lexx-polarnet-pl/AquaPi/Doc/html/hardware/ADS1115-ui.jpg

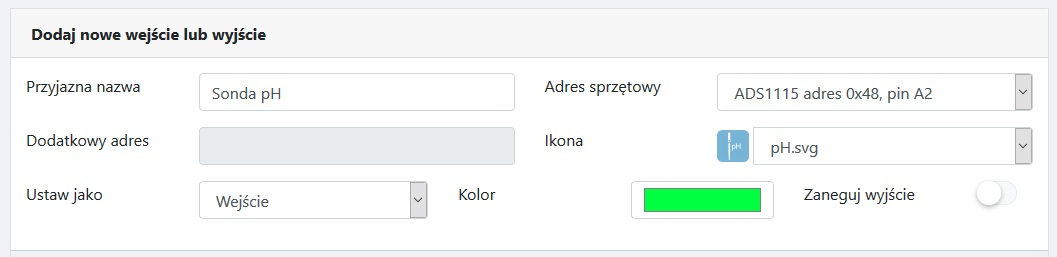
Doc/html/hardware/ADS1115-ui.jpg
