lexx-polarnet-pl/AquaPi/Doc/html/hardware/ADS1115.jpg

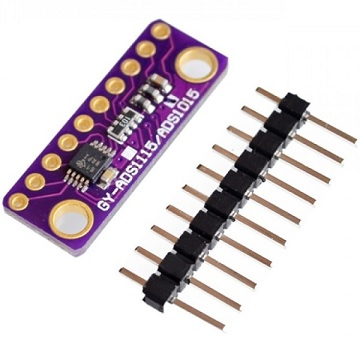
Doc/html/hardware/ADS1115.jpg
