lexx-polarnet-pl/AquaPi/Doc/html/hardware/AQUAPI_1.0-board.jpg

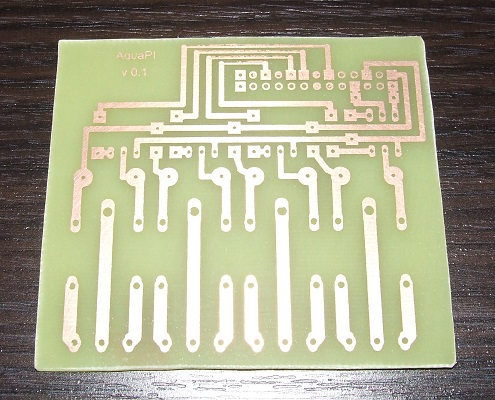
Doc/html/hardware/AQUAPI_1.0-board.jpg
