lexx-polarnet-pl/AquaPi/Doc/html/hardware/AQUAPI_1.0-complete.jpg

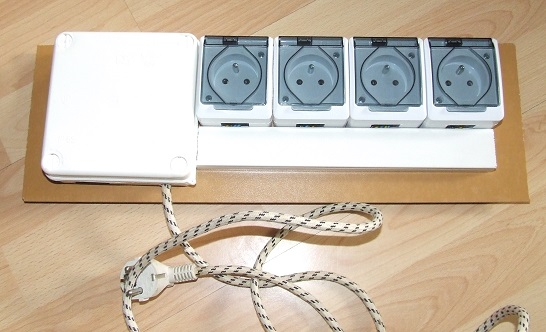
Doc/html/hardware/AQUAPI_1.0-complete.jpg
