lexx-polarnet-pl/AquaPi/Doc/html/hardware/AQUAPI_2.0_mainboard.jpg

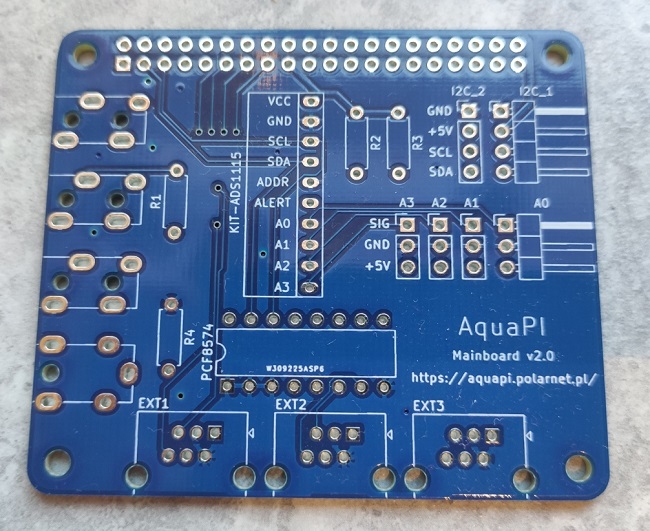
Doc/html/hardware/AQUAPI_2.0_mainboard.jpg
