lexx-polarnet-pl/AquaPi/Doc/html/hardware/AQUAPI_2.0_pwmboard.jpg

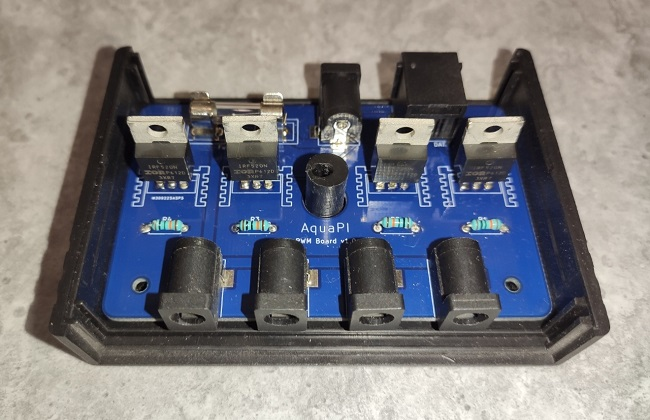
Doc/html/hardware/AQUAPI_2.0_pwmboard.jpg
