lexx-polarnet-pl/AquaPi/Doc/html/hardware/AQUAPI_connector_dc1.7.jpg

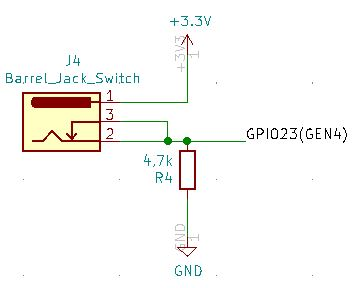
Doc/html/hardware/AQUAPI_connector_dc1.7.jpg
