lexx-polarnet-pl/AquaPi/Doc/html/hardware/AQUAPI_connector_rj12.jpg

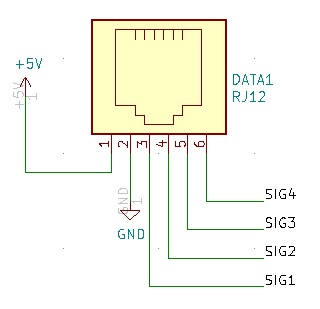
Doc/html/hardware/AQUAPI_connector_rj12.jpg
