lexx-polarnet-pl/AquaPi/Doc/html/hardware/DS18B20-pinout.jpg

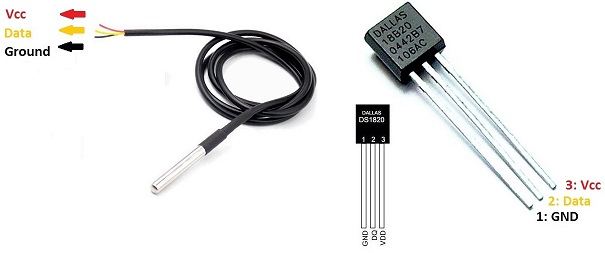
Doc/html/hardware/DS18B20-pinout.jpg
