lexx-polarnet-pl/AquaPi/Doc/html/hardware/DS18B20-ui.jpg

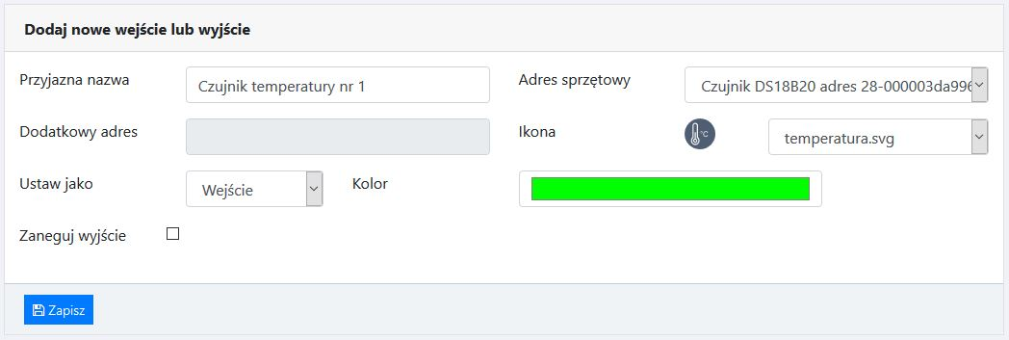
Doc/html/hardware/DS18B20-ui.jpg
