lexx-polarnet-pl/AquaPi/Doc/html/hardware/DS18B20.jpg

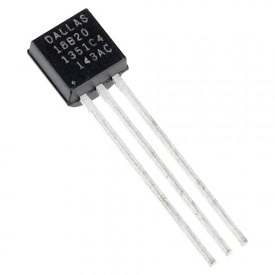
Doc/html/hardware/DS18B20.jpg
