lexx-polarnet-pl/AquaPi/Doc/html/hardware/GPIO1.jpg

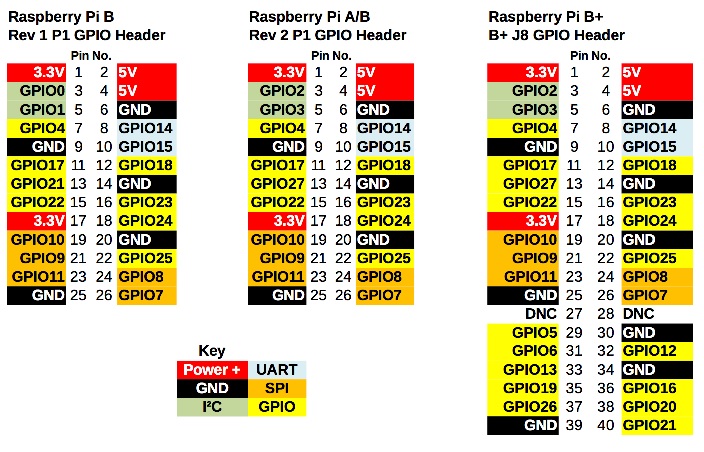
Doc/html/hardware/GPIO1.jpg
