lexx-polarnet-pl/AquaPi/Doc/html/hardware/GPIO2.jpg

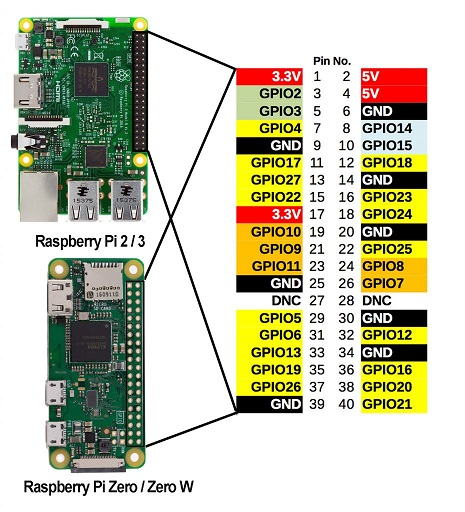
Doc/html/hardware/GPIO2.jpg
