lexx-polarnet-pl/AquaPi/Doc/html/hardware/MINIPH-ui.jpg

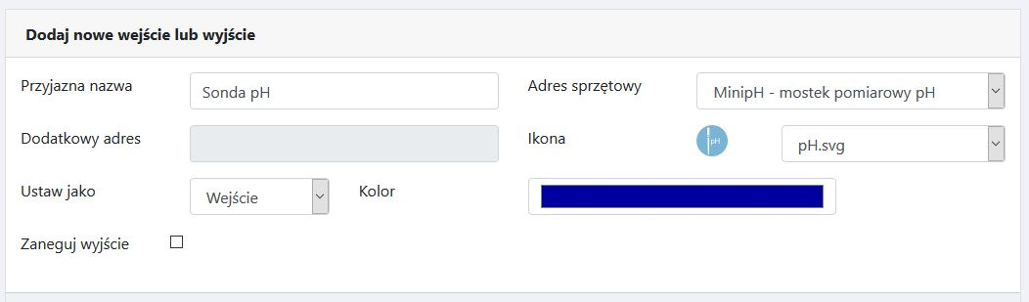
Doc/html/hardware/MINIPH-ui.jpg
