lexx-polarnet-pl/AquaPi/Doc/html/hardware/MINIPH-wire.jpg

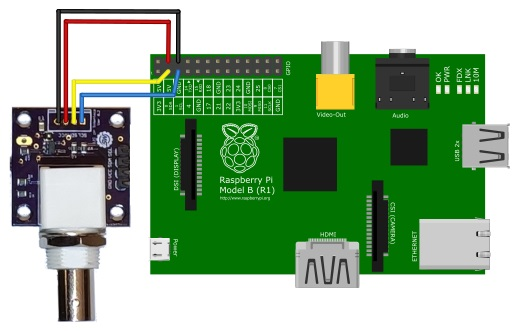
Doc/html/hardware/MINIPH-wire.jpg
