lexx-polarnet-pl/AquaPi/Doc/html/hardware/MINIPH.jpg

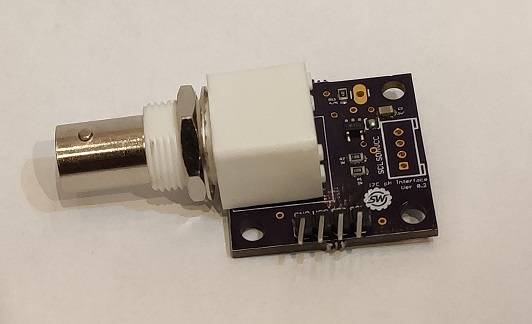
Doc/html/hardware/MINIPH.jpg
