lexx-polarnet-pl/AquaPi/Doc/html/hardware/MOSFET-wire.jpg

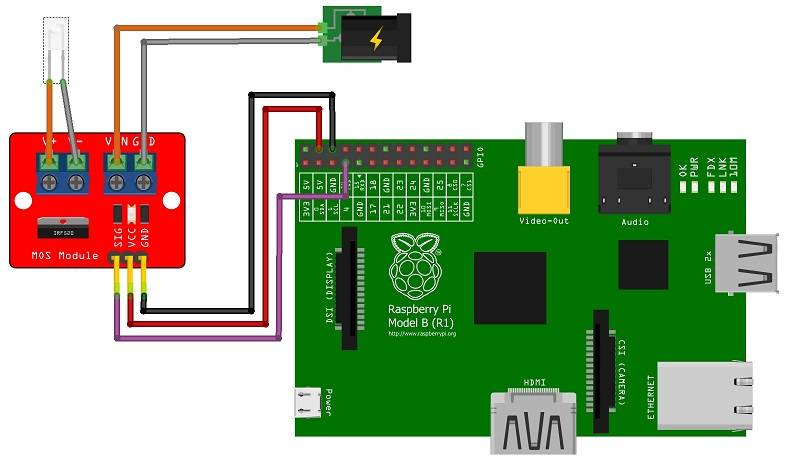
Doc/html/hardware/MOSFET-wire.jpg
