lexx-polarnet-pl/AquaPi/Doc/html/hardware/PCA9685-ui.jpg

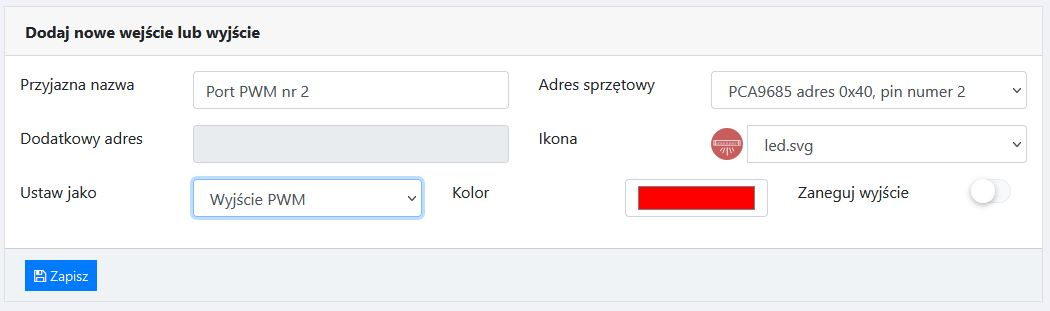
Doc/html/hardware/PCA9685-ui.jpg
