lexx-polarnet-pl/AquaPi/Doc/html/hardware/PCF8574-ui.jpg

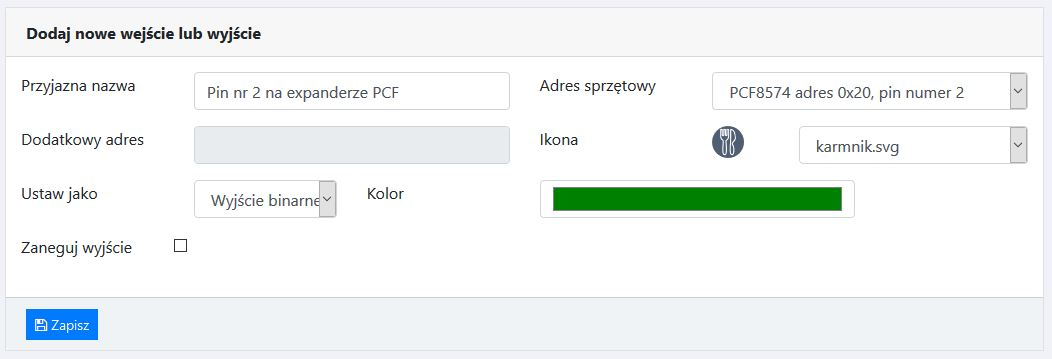
Doc/html/hardware/PCF8574-ui.jpg
