lexx-polarnet-pl/AquaPi/Doc/html/hardware/PCF8574-wire.jpg

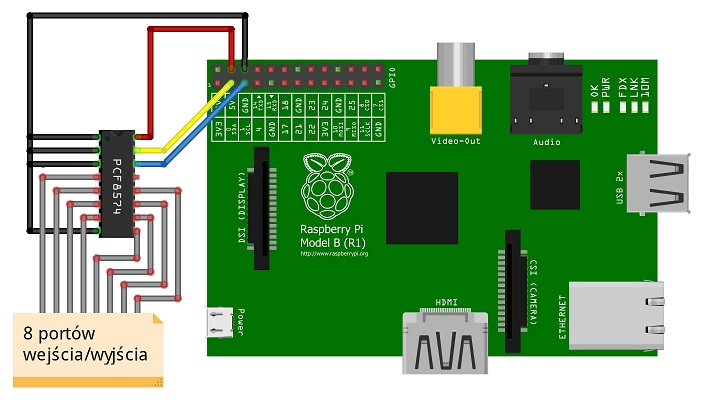
Doc/html/hardware/PCF8574-wire.jpg
