lexx-polarnet-pl/AquaPi/Doc/html/hardware/PCF8574.jpg

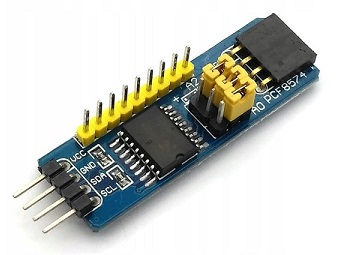
Doc/html/hardware/PCF8574.jpg
