lexx-polarnet-pl/AquaPi/Doc/html/hardware/PH_BRIDGE_SAMPLE.jpg

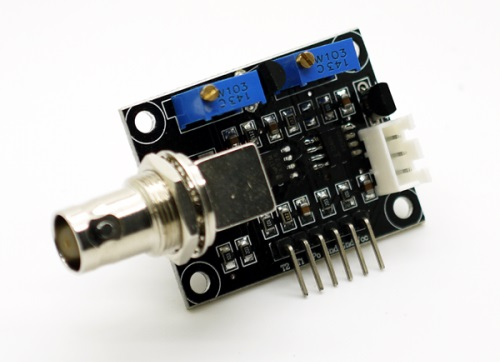
Doc/html/hardware/PH_BRIDGE_SAMPLE.jpg
