lexx-polarnet-pl/AquaPi/Doc/html/hardware/RELAY-1-wire.jpg

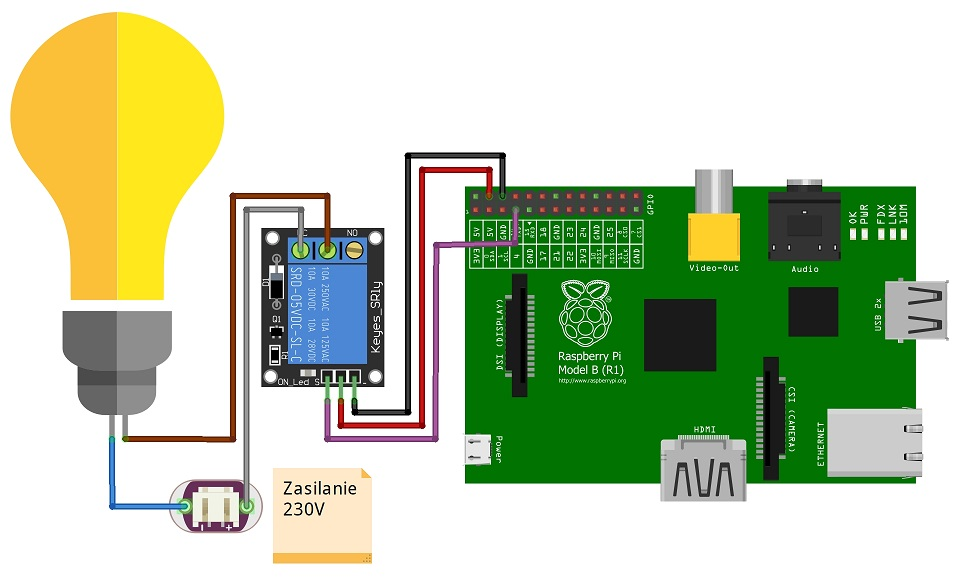
Doc/html/hardware/RELAY-1-wire.jpg
