lexx-polarnet-pl/AquaPi/Doc/html/hardware/RELAY-1.jpg

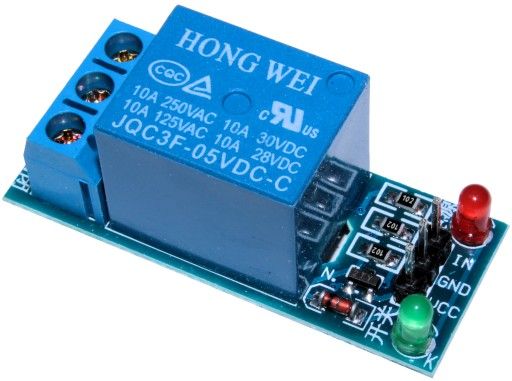
Doc/html/hardware/RELAY-1.jpg
