lexx-polarnet-pl/AquaPi/Doc/html/hardware/RELAY-8-sample.jpg

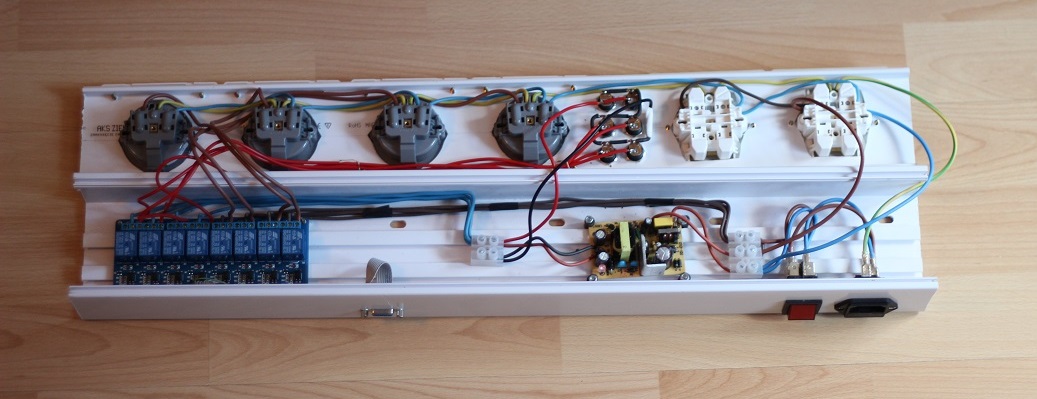
Doc/html/hardware/RELAY-8-sample.jpg
