lexx-polarnet-pl/AquaPi/Doc/html/hardware/RELAY-8.jpg

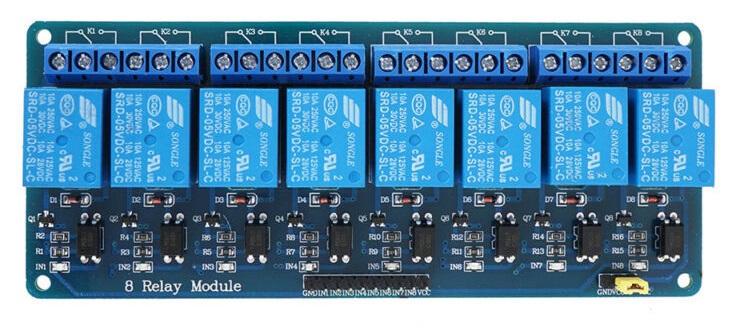
Doc/html/hardware/RELAY-8.jpg
