lexx-polarnet-pl/AquaPi/Doc/html/hardware/RELAY-SSR-sample.jpg

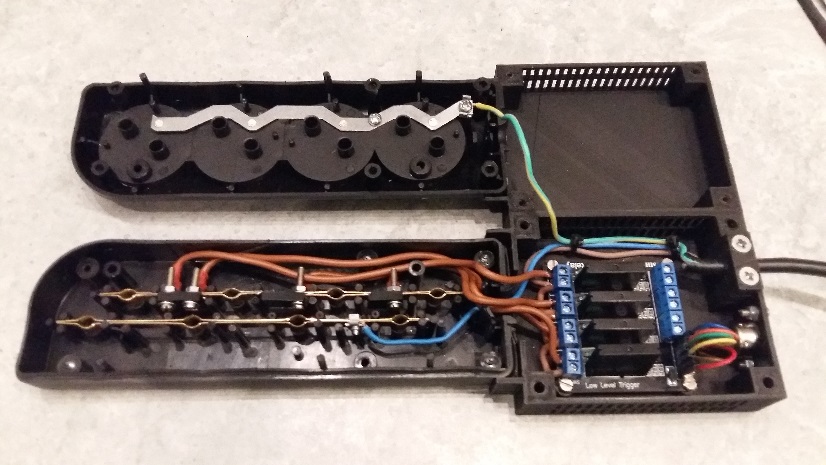
Doc/html/hardware/RELAY-SSR-sample.jpg
