lexx-polarnet-pl/AquaPi/Doc/html/hardware/RELAY-SSR.jpg

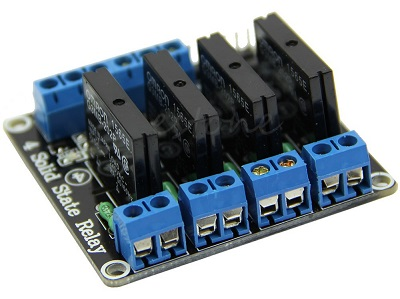
Doc/html/hardware/RELAY-SSR.jpg
