lexx-polarnet-pl/AquaPi/Doc/html/hardware/TRIAK.jpg

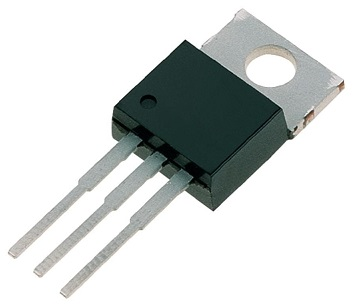
Doc/html/hardware/TRIAK.jpg
