lexx-polarnet-pl/AquaPi/Doc/sensory temp - aquamat.PNG

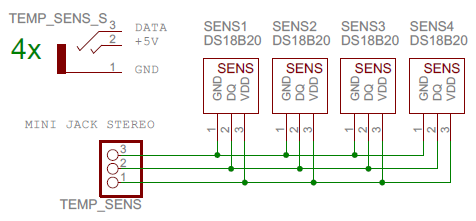
Doc/sensory temp - aquamat.PNG
