lexx-polarnet-pl/AquaPi/Doc/html/hardware/AQUAPI_1.0-assembled.jpg

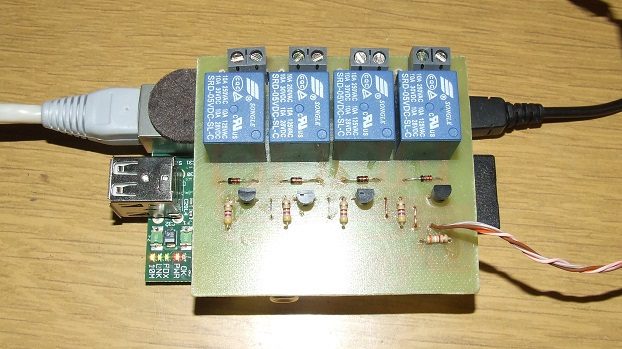
Doc/html/hardware/AQUAPI_1.0-assembled.jpg
