lexx-polarnet-pl/AquaPi/Doc/html/hardware/AQUAPI_2.0-assembled.jpg

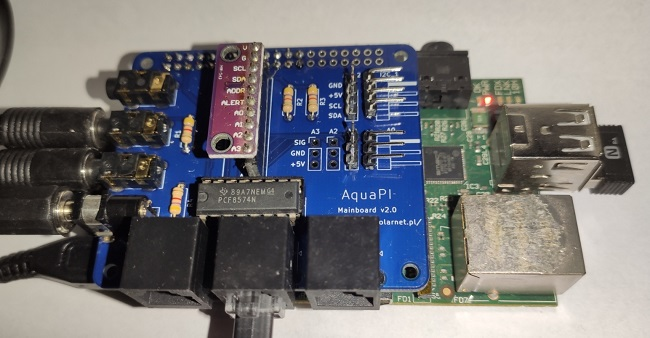
Doc/html/hardware/AQUAPI_2.0-assembled.jpg
