lexx-polarnet-pl/AquaPi/Doc/html/install/RASPI-CONFIG.jpg

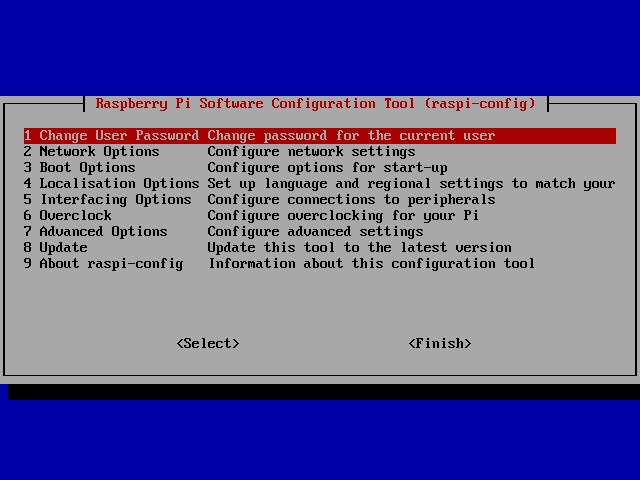
Doc/html/install/RASPI-CONFIG.jpg
