lexx-polarnet-pl/AquaPi/Doc/html/install/RASPI-I2C-1W.jpg

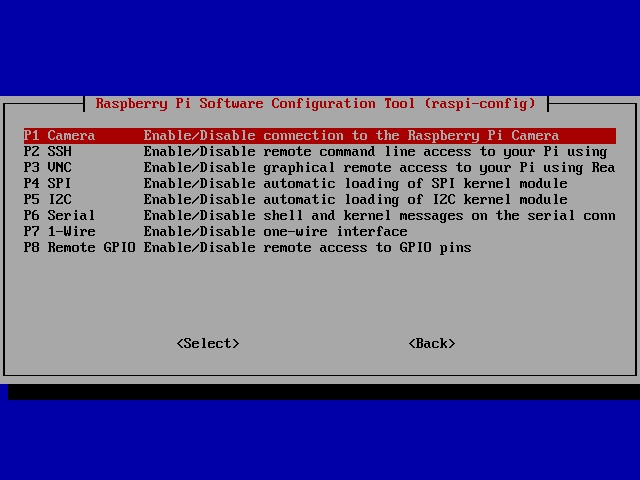
Doc/html/install/RASPI-I2C-1W.jpg
