lexx-polarnet-pl/AquaPi/Doc/html/install/WEBUI-1ST_RUN.jpg

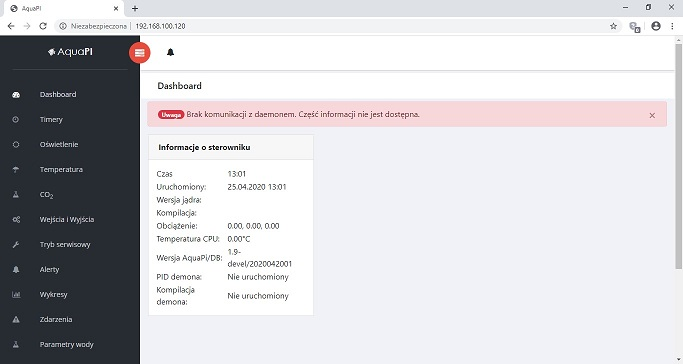
Doc/html/install/WEBUI-1ST_RUN.jpg
