lexx-polarnet-pl/AquaPi/Doc/html/install/WIN32_DISK_IMAGER.jpg

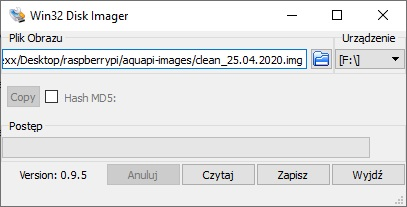
Doc/html/install/WIN32_DISK_IMAGER.jpg
