lexx-polarnet-pl/AquaPi/Software/daemon/temperature.c

/*
 * AquaPi - sterownik akwariowy oparty o Raspberry Pi
 *
 * Copyright (C) 2012-2018 AquaPi Developers
 *
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
 */

struct _temperature {
	double  tmax;
	double  hc;
	double  tmin;
	double  hg;
	double  ncor;
	double  actual;
	int interface_heat;
	int interface_cool;
	int interface_sensor;	
} temperature;

void ModTemperature_ReadSettings() {
	char buff[200];
	DB_GetSetting("temp_tmax",buff);
	temperature.tmax = atof(buff);
	DB_GetSetting("temp_hc",buff);
	temperature.hc = atof(buff);	
	DB_GetSetting("temp_tmin",buff);
	temperature.tmin = atof(buff);	
	DB_GetSetting("temp_hg",buff);
	temperature.hg = atof(buff);	
	DB_GetSetting("temp_ncor",buff);
	temperature.ncor = atof(buff);	

	DB_GetSetting("temp_interface_heat",buff);
	temperature.interface_heat = atof(buff);	
	DB_GetSetting("temp_interface_cool",buff);
	temperature.interface_cool = atof(buff);	
	DB_GetSetting("temp_interface_sensor",buff);
	temperature.interface_sensor = atof(buff);	
	// wymuś stan nieustalony
	temperature.actual = -100;
}

void ModTemperature_Process() {

	//Odczytajmy aktualną temperaturę
	temperature.actual = GetValFromInterface(temperature.interface_sensor);

	//Czy włączamy grzanie?
	if (temperature.actual < temperature.tmin) {
		SetInterfaceNewVal(temperature.interface_heat,1);
	}
	//Czy wyłączamy grzanie?
	if (temperature.actual > temperature.tmin + temperature.hg) {
		SetInterfaceNewVal(temperature.interface_heat,0);
	}
	//Czy włączamy chłodzenie?
	if (temperature.actual > temperature.tmax) {
		SetInterfaceNewVal(temperature.interface_cool,1);
	}
	//Czy wyłączamy chłodzenie?
	if (temperature.actual < temperature.tmax - temperature.hc) {
		SetInterfaceNewVal(temperature.interface_cool,0);
	}

	// zabezpieczenie na wypadek awarii sensorów
	if (temperature.actual <= -100) {
		//w przypadku awarii wyłącz grzanie i chłodzenie
		SetInterfaceNewVal(temperature.interface_heat,0);
		SetInterfaceNewVal(temperature.interface_cool,0);
	} 
}

void ModTemperature_Debug() { // informacje devel
	char buff[200];
	Log("═════════════════ Zrzut danych modułu TEMPERATURE ═════════════════",E_DEV);	
	sprintf(buff,"Tact %.1f°C, Tmin: %.1f°C, Hg: %.1f°C, Hc: %.1f°C, Tmax: %.1f°C, Tncor: %.1f°C", \
		temperature.actual,temperature.tmin,temperature.hg,temperature.hc,temperature.tmax,temperature.ncor);
	Log(buff,E_DEV);	
}
